TinyCircuits/TinyCircuits-TinyShield-NRF24L01-ASD2163/images/ASD2163-R-Tutorial-Image-01.jpg

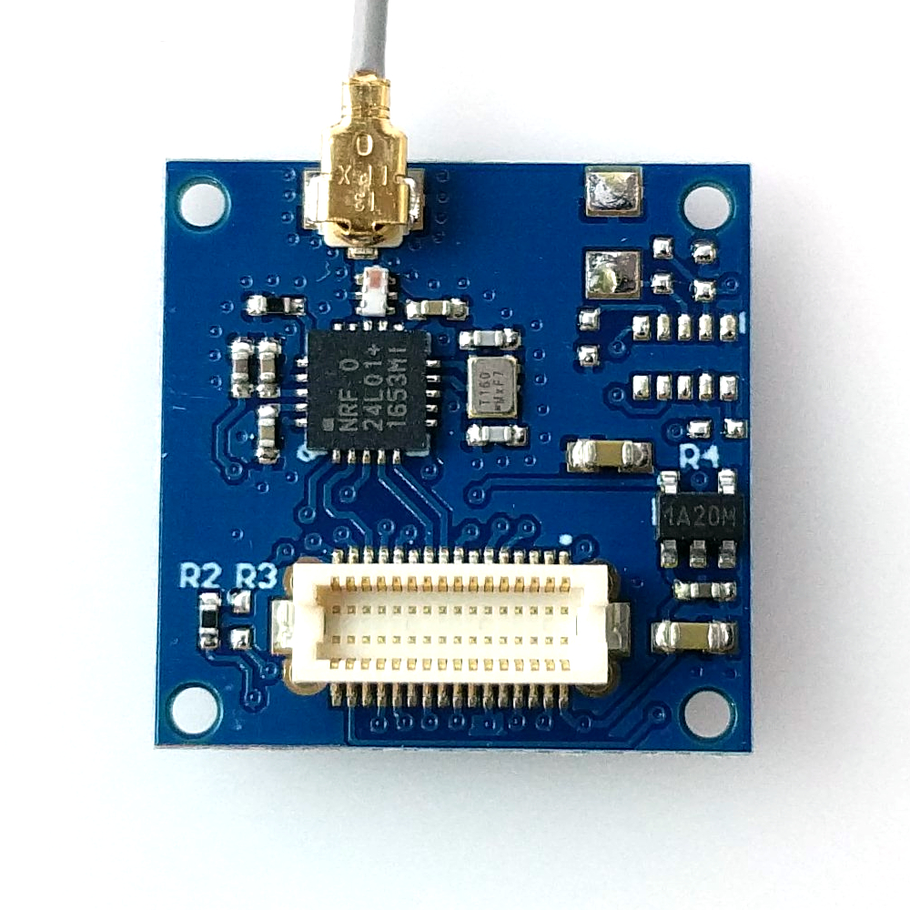
images/ASD2163-R-Tutorial-Image-01.jpg
